agkeck-iivi/internet_radio_v2/main/lvgl_ssd1306_setup.h

#ifndef LVGL_SSD1306_SETUP_H
#define LVGL_SSD1306_SETUP_H

#include "lvgl.h"

#ifdef __cplusplus
extern "C" {
#endif

/**
 * @brief Initializes the SSD1306 display, LVGL, and related tasks.
 * @return A pointer to the created LVGL display.
 */
lv_display_t* lvgl_ssd1306_setup(void);

#ifdef __cplusplus
}
#endif

#endif // LVGL_SSD1306_SETUP_H
